tvumcc/clock/schematics/clock/clock.kicad_sch

## KiCad design schematics/clock/clock.kicad_sch (2025-04-03)

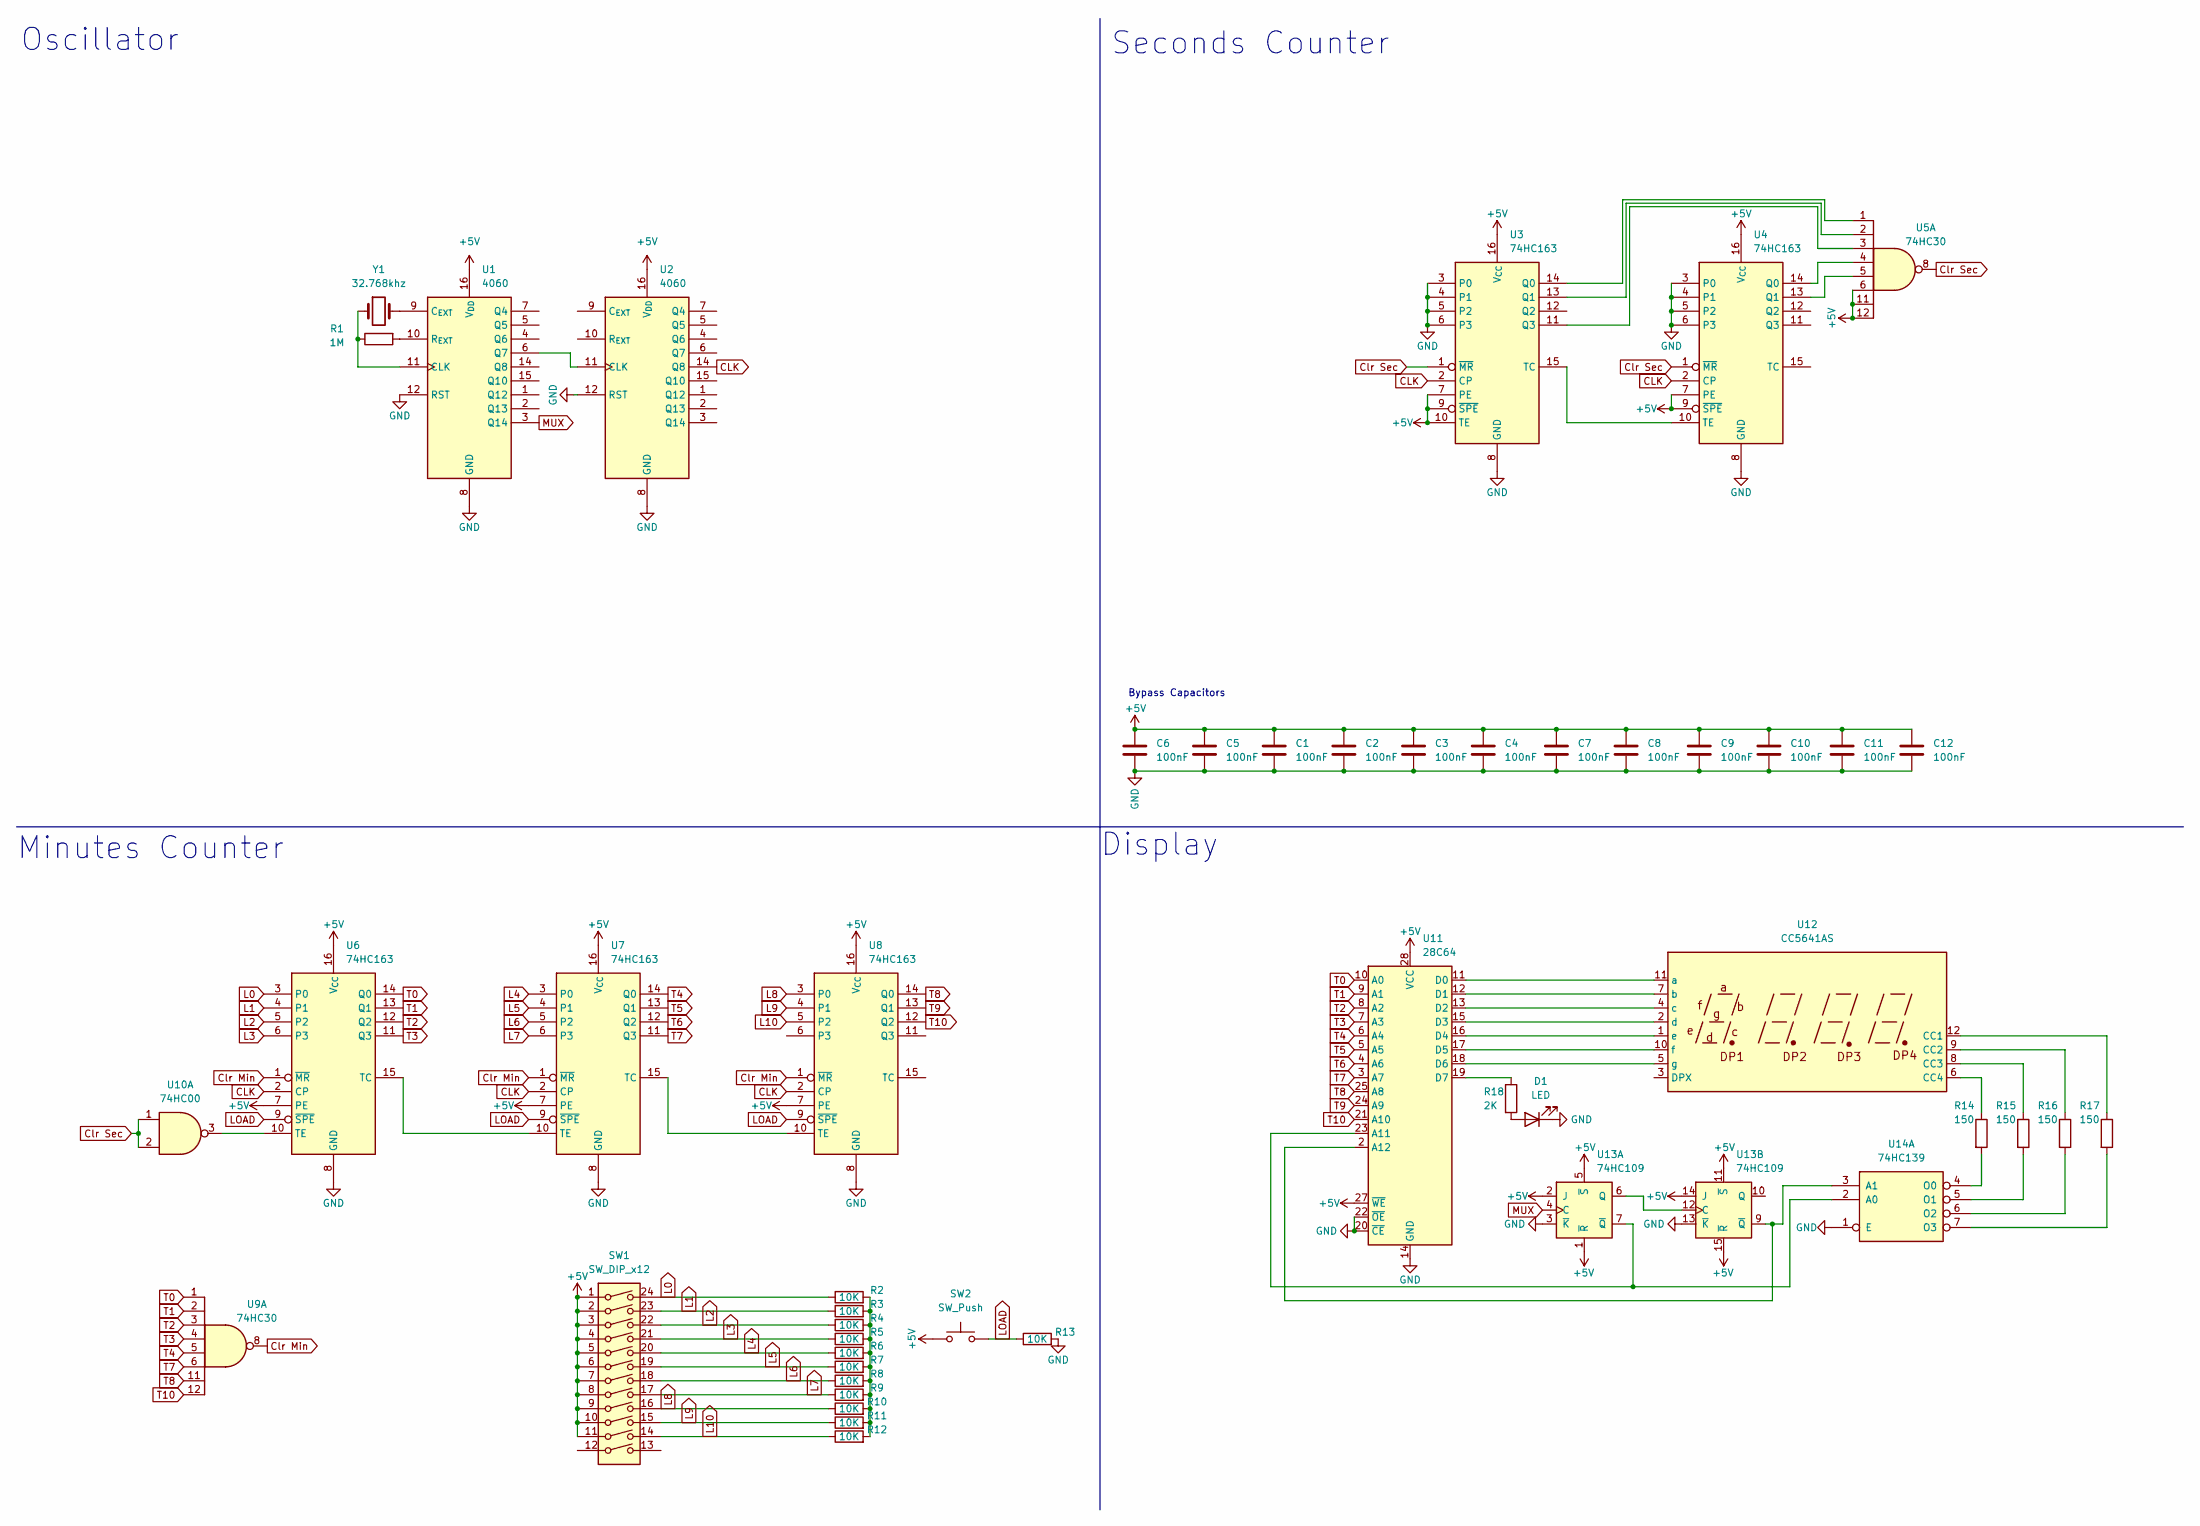
[picture p5: schematic clock.kicad_sch]

Parts:
C1, C2, C3, C4, C5, C6, C7, C8, C9, C10, C11, C12: 100nF
D1: LED
R1: 1M
R2, R3, R4, R5, R6, R7, R8, R9, R10, R11, R12, R13: 10K
R14, R15, R16, R17: 150
R18: 2K
SW1: SW_DIP_x12
SW2: SW_Push
U1, U2: 4060
U3, U4, U6, U7, U8: 74HC163
U5, U9: 74HC30
U10: 74HC00; DIP-14_W7.62mm
U11: 28C64; DIP-28_W15.24mm
U12: CC5641AS; CA56-12SRWA
U13: 74HC109
U14: 74HC139
Y1: 32.768khz

Connections:
+5V: C1.1, C2.1, C3.1, C4.1, C5.1, C6.1, C7.1, C8.1, C9.1, C10.1, C11.1, C12.1, SW1.1, SW1.2, SW1.3, SW1.4, SW1.5, SW1.6, SW1.7, SW1.8, SW1.9, SW1.10, SW1.11, SW2.1, U1.16 (V_{DD}), U2.16 (V_{DD}), U3.7 (PE), U3.9 (~SPE), U3.10 (TE), U3.16 (V_{CC}), U4.7 (PE), U4.9 (~SPE), U4.16 (V_{CC}), U5.6, U5.11, U5.12, U6.7 (PE), U6.16 (V_{CC}), U7.7 (PE), U7.16 (V_{CC}), U8.7 (PE), U8.16 (V_{CC}), U11.27 (~WE), U11.28 (VCC), U13.1 (~R), U13.2 (J), U13.5 (~S), U13.11 (~S), U13.14 (J), U13.15 (~R)
CLK: U2.14 (Q8), U3.2 (CP), U4.2 (CP), U6.2 (CP), U7.2 (CP), U8.2 (CP)
Clr Min: U6.1 (~MR), U7.1 (~MR), U8.1 (~MR), U9.8
Clr Sec: U3.1 (~MR), U4.1 (~MR), U5.8, U10.1, U10.2
GND: C1.2, C2.2, C3.2, C4.2, C5.2, C6.2, C7.2, C8.2, C9.2, C10.2, C11.2, C12.2, D1.1 (K), R13.2, U1.8 (GND), U1.12 (RST), U2.8 (GND), U2.12 (RST), U3.3 (P0), U3.4 (P1), U3.5 (P2), U3.6 (P3), U3.8 (GND), U4.3 (P0), U4.4 (P1), U4.5 (P2), U4.6 (P3), U4.8 (GND), U6.8 (GND), U7.8 (GND), U8.8 (GND), U11.14 (GND), U11.20 (~CE), U11.22 (~OE), U13.3 (~K), U13.13 (~K), U14.1 (E)
L0: R2.1, SW1.24, U6.3 (P0)
L1: R3.1, SW1.23, U6.4 (P1)
L2: R4.1, SW1.22, U6.5 (P2)
L3: R5.1, SW1.21, U6.6 (P3)
L4: R6.1, SW1.20, U7.3 (P0)
L5: R7.1, SW1.19, U7.4 (P1)
L6: R8.1, SW1.18, U7.5 (P2)
L7: R9.1, SW1.17, U7.6 (P3)
L8: R10.1, SW1.16, U8.3 (P0)
L9: R11.1, SW1.15, U8.4 (P1)
L10: R12.1, SW1.14, U8.5 (P2)
LOAD: R13.1, SW2.2, U6.9 (~SPE), U7.9 (~SPE), U8.9 (~SPE)
MUX: U1.3 (Q14), U13.4 (C)
unnamed: D1.2 (A), R18.2
unnamed: R1.1, U1.11 (CLK), Y1.1
unnamed: R1.2, U1.10 (R_{EXT})
unnamed: R2.2, R3.2, R4.2, R5.2, R6.2, R7.2, R8.2, R9.2, R10.2, R11.2, R12.2
unnamed: R14.1, U12.6 (CC4)
unnamed: R14.2, U14.4 (O0)
unnamed: R15.1, U12.8 (CC3)
unnamed: R15.2, U14.5 (O1)
unnamed: R16.1, U12.9 (CC2)
unnamed: R16.2, U14.6 (O2)
unnamed: R17.1, U12.12 (CC1)
unnamed: R17.2, U14.7 (O3)
unnamed: R18.1, U11.19 (D7)
unnamed: U1.6 (Q7), U2.11 (CLK)
unnamed: U1.9 (C_{EXT}), Y1.2
unnamed: U3.11 (Q3), U5.3
unnamed: U3.13 (Q1), U5.2
unnamed: U3.14 (Q0), U5.1
unnamed: U3.15 (TC), U4.10 (TE)
unnamed: U4.13 (Q1), U5.5
unnamed: U4.14 (Q0), U5.4
unnamed: U6.15 (TC), U7.10 (TE)
unnamed: U7.15 (TC), U8.10 (TE)
unnamed: U6.10 (TE), U10.3
unnamed: U11.2 (A12), U13.9 (~Q), U14.3 (A1)
unnamed: U11.11 (D0), U12.11 (a)
unnamed: U11.12 (D1), U12.7 (b)
unnamed: U11.13 (D2), U12.4 (c)
unnamed: U11.15 (D3), U12.2 (d)
unnamed: U11.16 (D4), U12.1 (e)
unnamed: U11.17 (D5), U12.10 (f)
unnamed: U11.18 (D6), U12.5 (g)
unnamed: U11.23 (A11), U13.7 (~Q), U14.2 (A0)
unnamed: U13.6 (Q), U13.12 (C)
T0: U6.14 (Q0), U9.1, U11.10 (A0)
T1: U6.13 (Q1), U9.2, U11.9 (A1)
T2: U6.12 (Q2), U9.3, U11.8 (A2)
T3: U6.11 (Q3), U9.4, U11.7 (A3)
T4: U7.14 (Q0), U9.5, U11.6 (A4)
T5: U7.13 (Q1), U11.5 (A5)
T6: U7.12 (Q2), U11.4 (A6)
T7: U7.11 (Q3), U9.6, U11.3 (A7)
T8: U8.14 (Q0), U9.11, U11.25 (A8)
T9: U8.13 (Q1), U11.24 (A9)
T10: U8.12 (Q2), U9.12, U11.21 (A10)

Notes on the sheet:
Display
Oscillator
Bypass Capacitors
Seconds Counter
Minutes Counter
